tmhglnd/abstraction-minified/images/img2.jpeg

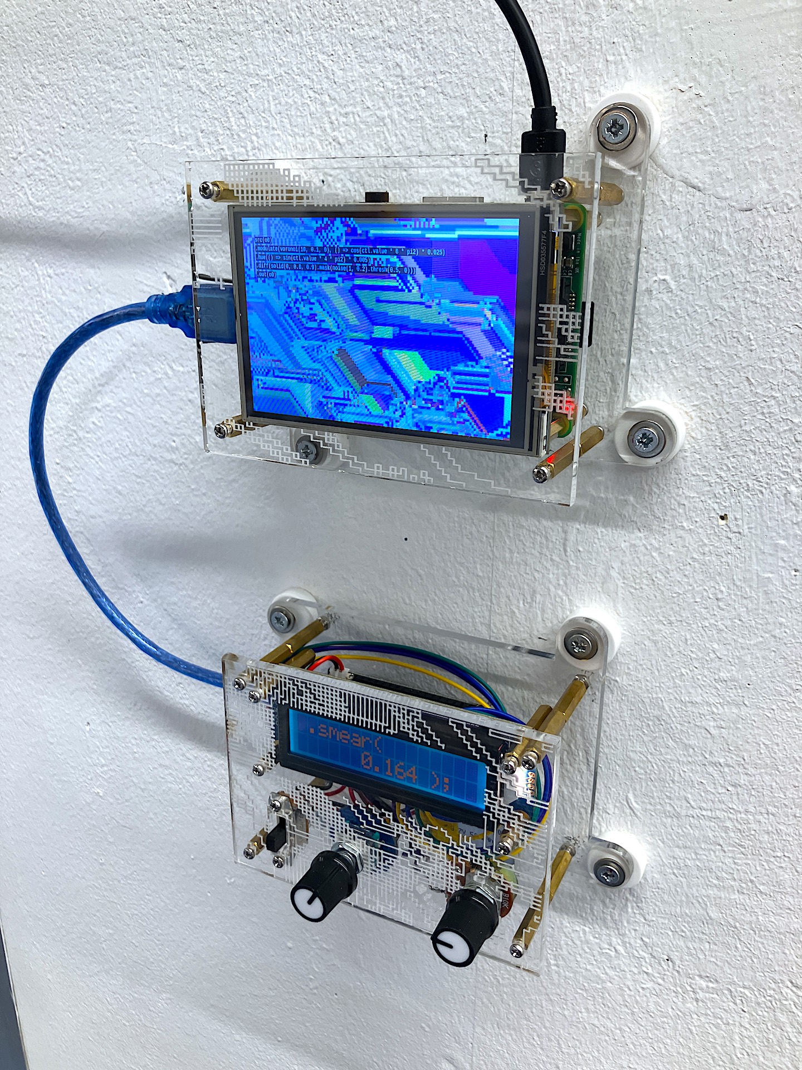
images/img2.jpeg
