tmhglnd/abstraction-minified/images/img3.jpeg

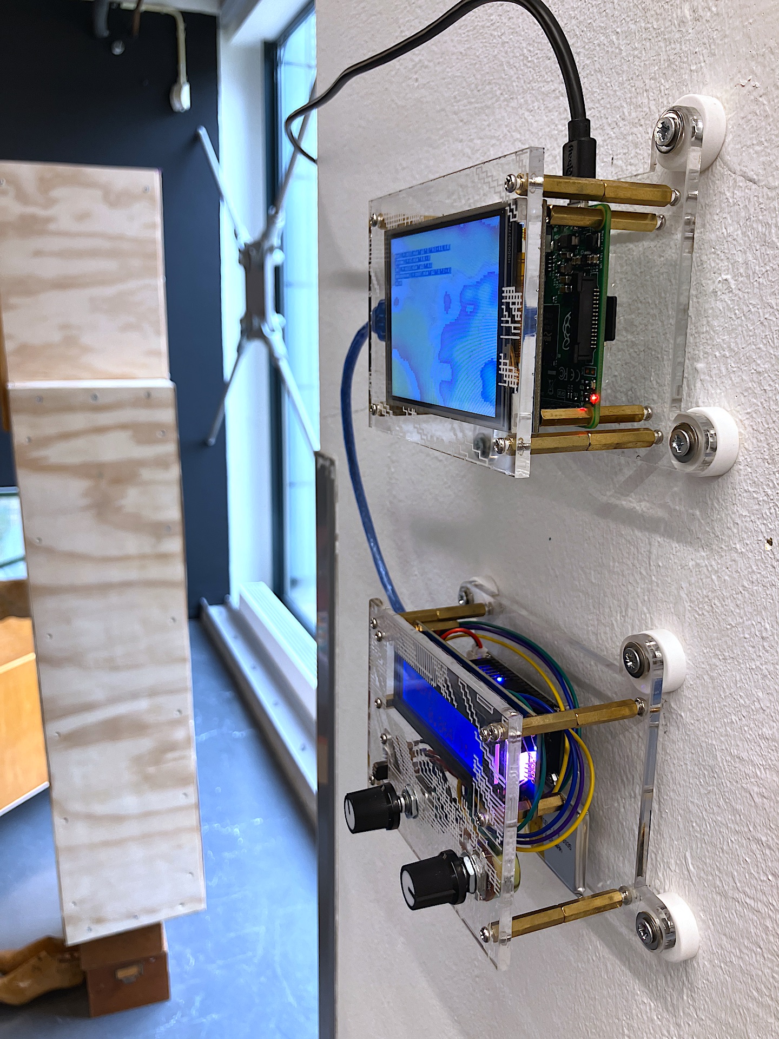
images/img3.jpeg
