tmhglnd/abstraction-minified/images/img4.jpeg

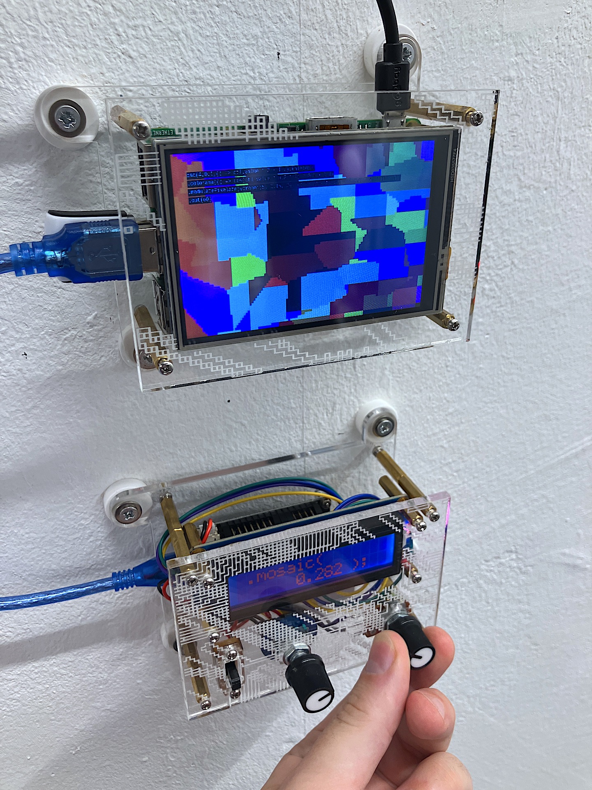
images/img4.jpeg
